brickbots/aball/photos/finished_double.jpeg

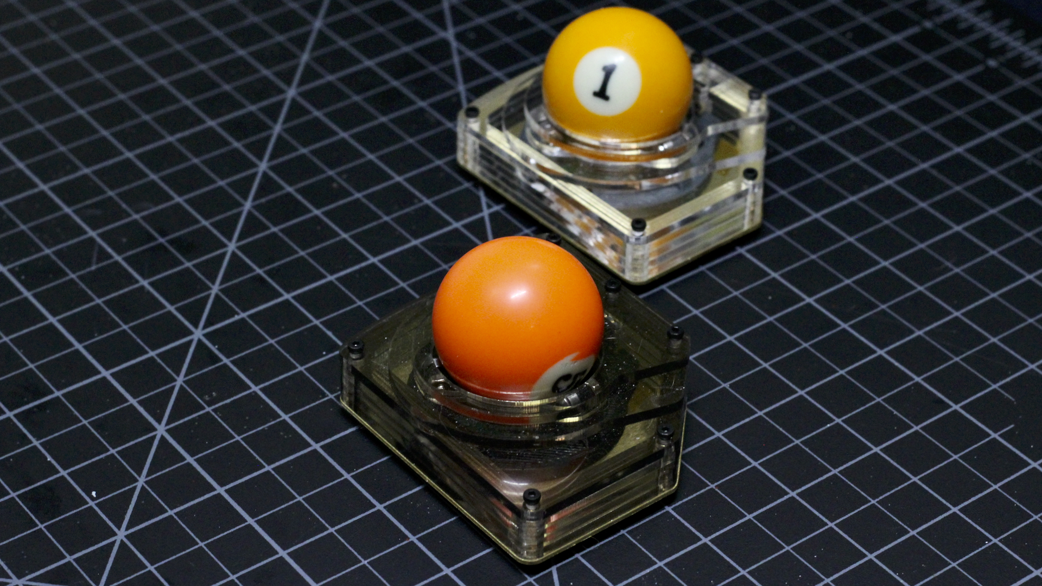
photos/finished_double.jpeg
