brickbots/aball/photos/kyria_fit.jpeg

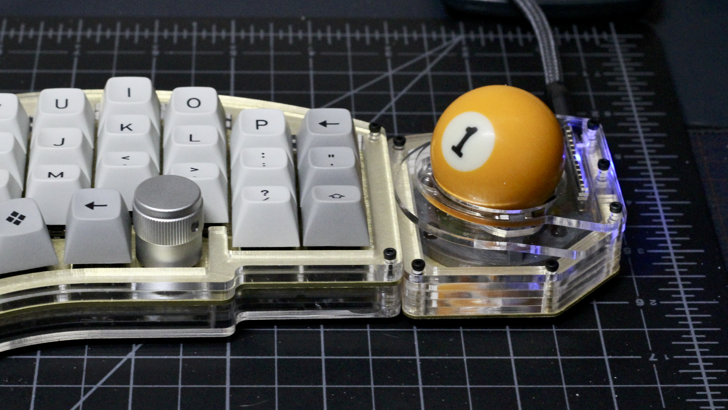
photos/kyria_fit.jpeg
