brickbots/aball/photos/kyria_mid.jpeg

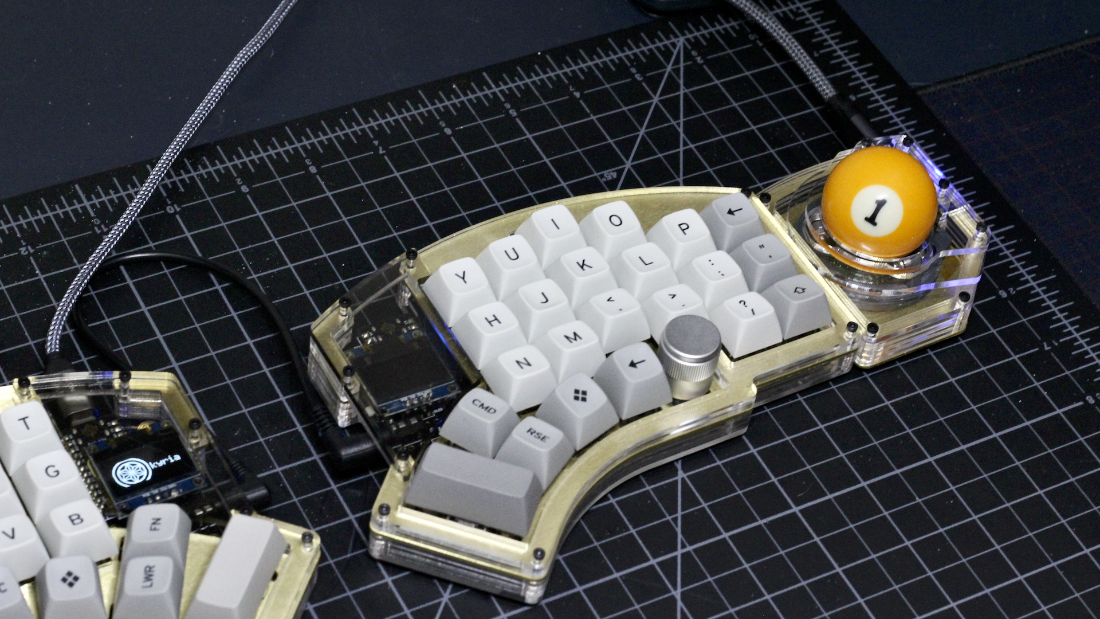
photos/kyria_mid.jpeg
