brickbots/aball/case/laser_cut_stacked/top_a.dxf

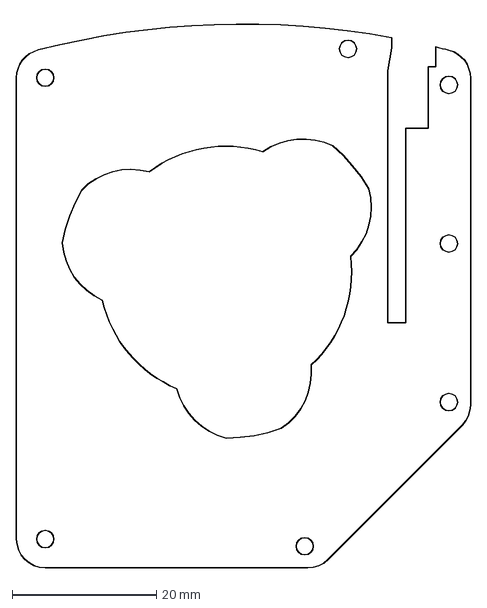
[picture p38: CAD file, 2020-06-13]
case/laser_cut_stacked/top_a.dxf
63.0 x 76.6 mm
