brickbots/aball/photos/build_guide/aball_build_guide_20.jpeg

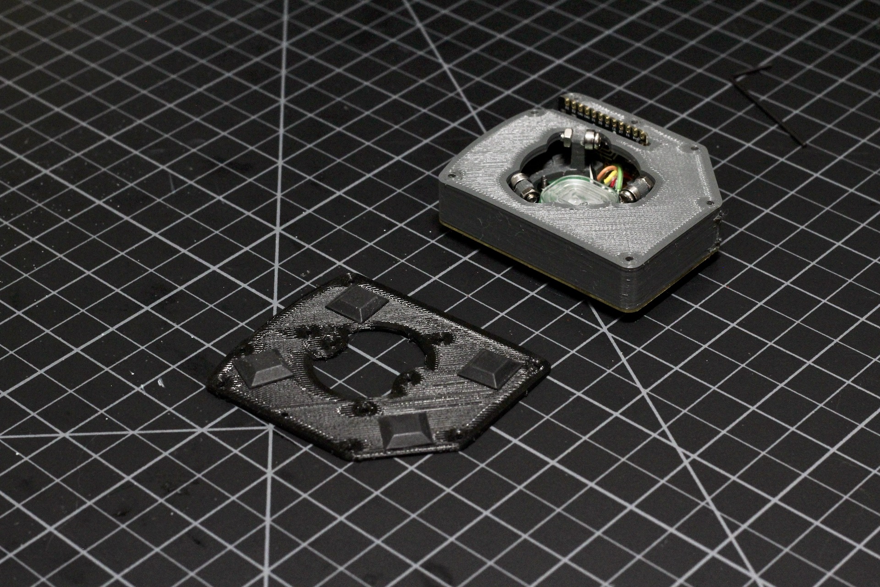
photos/build_guide/aball_build_guide_20.jpeg
