brickbots/aball/photos/build_guide/aball_build_guide_25.jpeg

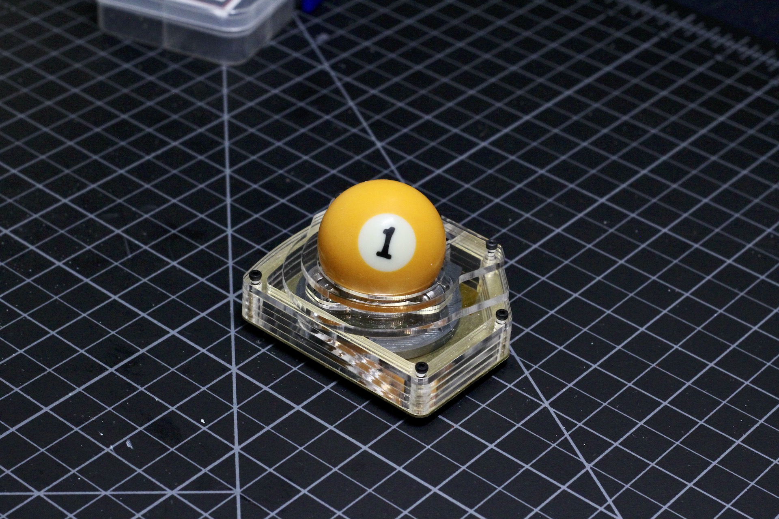
photos/build_guide/aball_build_guide_25.jpeg
